spider-tronix/arboc/simulationExports/gazebo/stl/end.stl

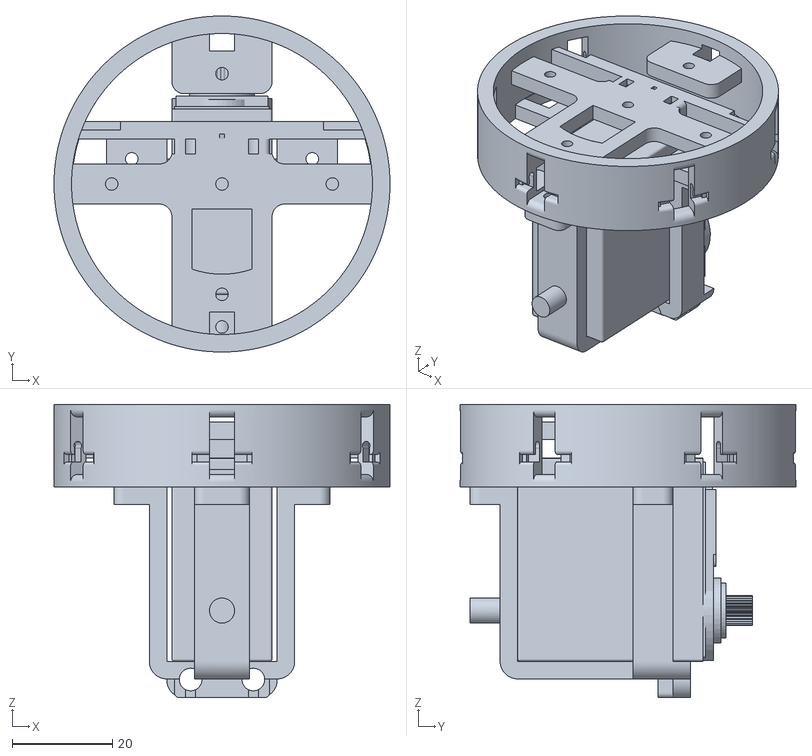
[picture p20: CAD file, 2019-06-01]
simulationExports/gazebo/stl/end.stl
67.0 x 67.0 x 58.5
