spider-tronix/arboc/mechanicalDesign/3DprintedParts/type4.step

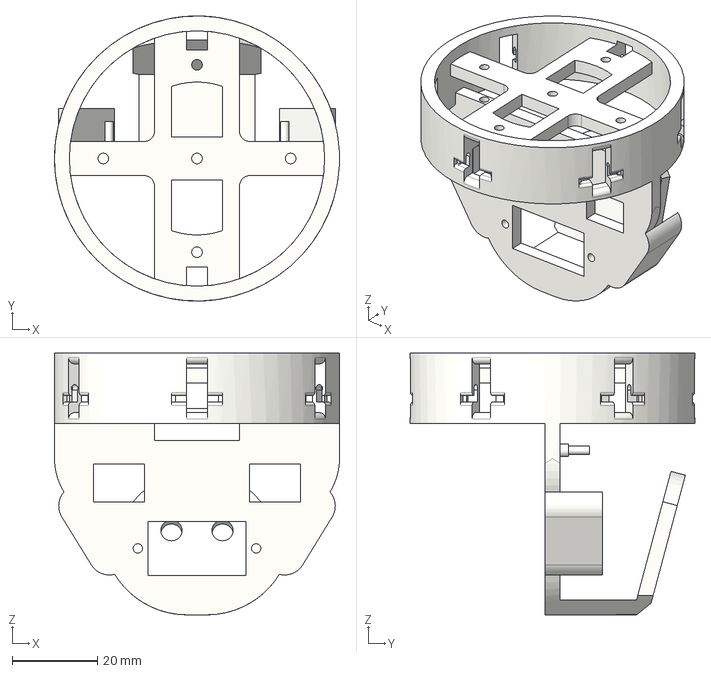
[picture p21: CAD file, 2019-06-01]
mechanicalDesign/3DprintedParts/type4.step
67.0 x 67.0 x 61.5 mm
