spider-tronix/arboc/mechanicalDesign/solidworks/iges/tailLink.SLDPRT

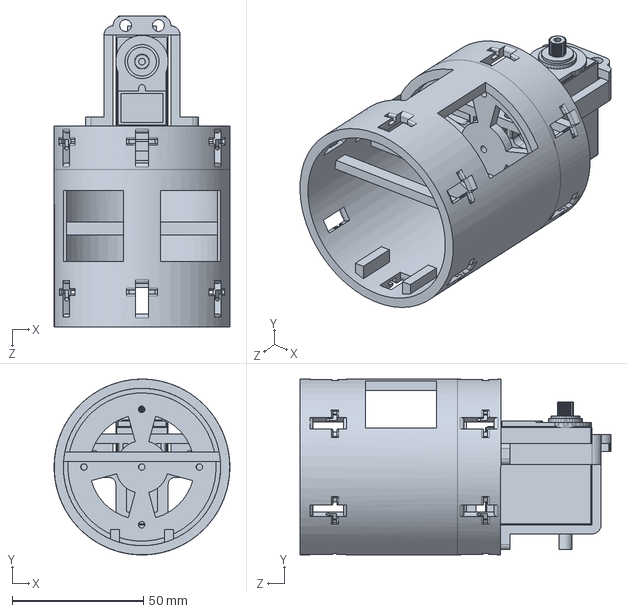
[picture p22: CAD file, 2019-06-01]
mechanicalDesign/solidworks/iges/tailLink.SLDPRT
67.0 x 67.0 x 118.5 mm
