spider-tronix/arboc/mechanicalDesign/solidworks/step/lowerBracket.step

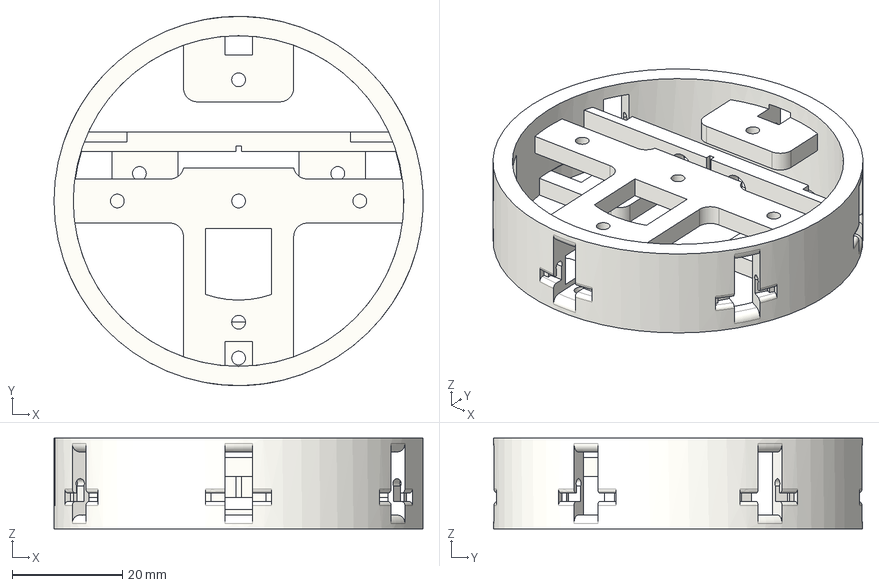
[picture p23: CAD file, 2019-06-01]
mechanicalDesign/solidworks/step/lowerBracket.step
67.0 x 67.0 x 16.5 mm
