spider-tronix/arboc/simulationExports/vrep/stl/moduleCollider.stl

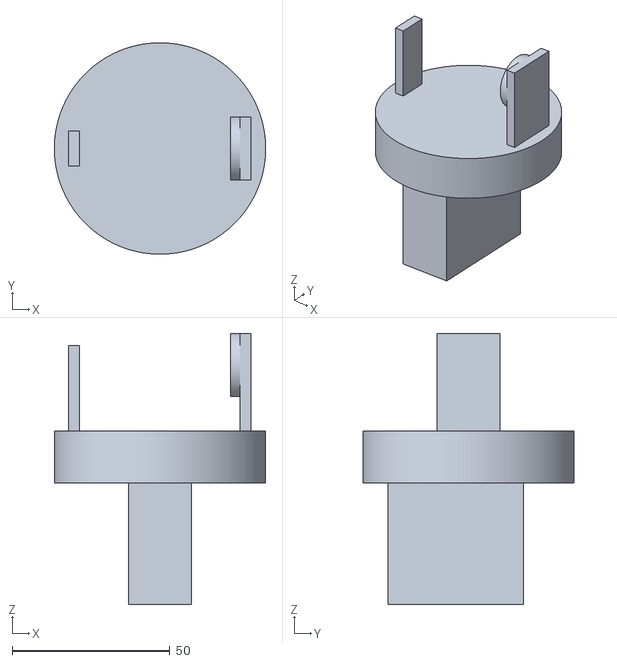
[picture p24: CAD file, 2019-06-01]
simulationExports/vrep/stl/moduleCollider.stl
67.0 x 67.0 x 85.9
