spider-tronix/arboc/mechanicalDesign/3DprintedParts/type2.step

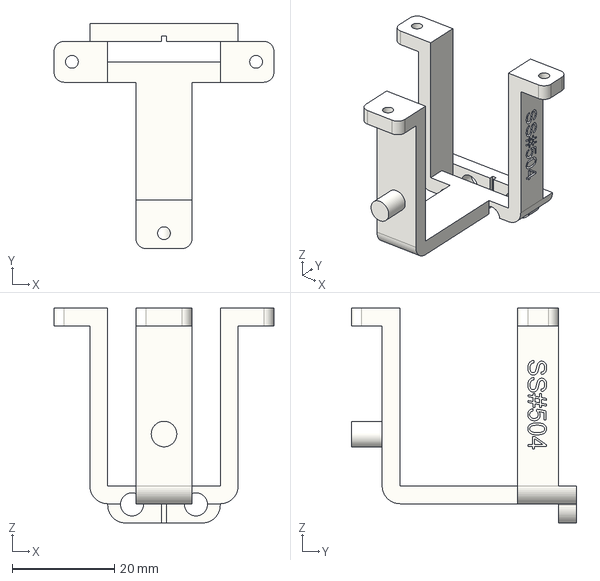
[picture p25: CAD file, 2019-06-01]
mechanicalDesign/3DprintedParts/type2.step
43.0 x 44.0 x 42.0 mm
