spider-tronix/arboc/mechanicalDesign/solidworks/sldprt/head.SLDPRT

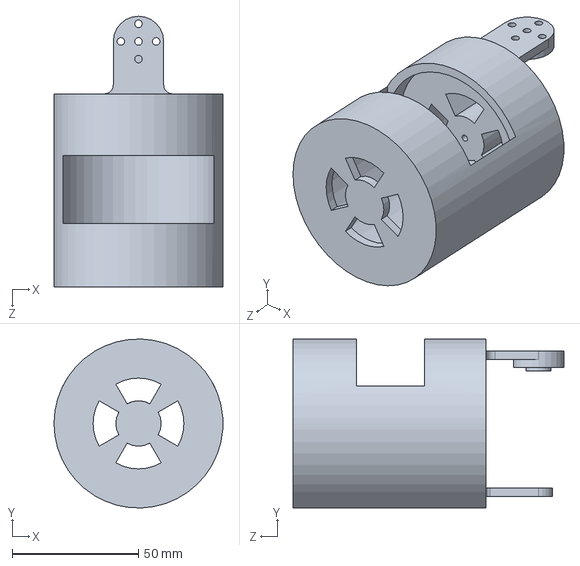
[picture p26: CAD file, 2019-06-01]
mechanicalDesign/solidworks/sldprt/head.SLDPRT
67.0 x 67.0 x 107.3 mm
