spider-tronix/arboc/mechanicalDesign/solidworks/step/middleBracket.step

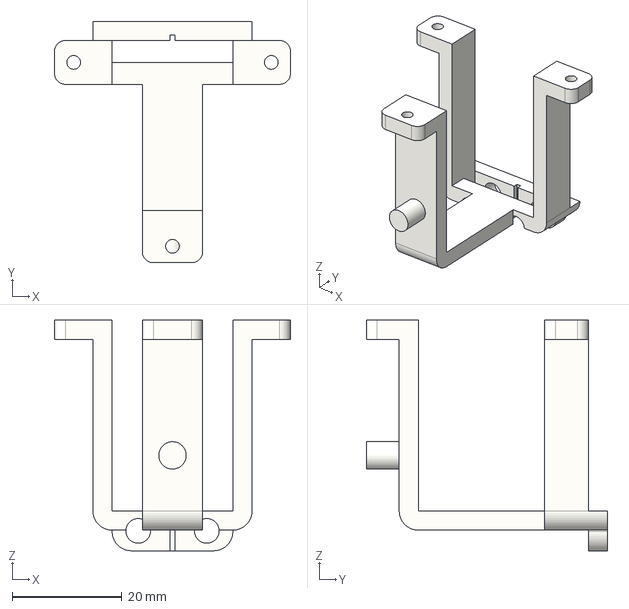
[picture p27: CAD file, 2019-06-01]
mechanicalDesign/solidworks/step/middleBracket.step
43.0 x 44.0 x 42.0 mm
