spider-tronix/arboc/simulationExports/gazebo/stl/topModule.stl

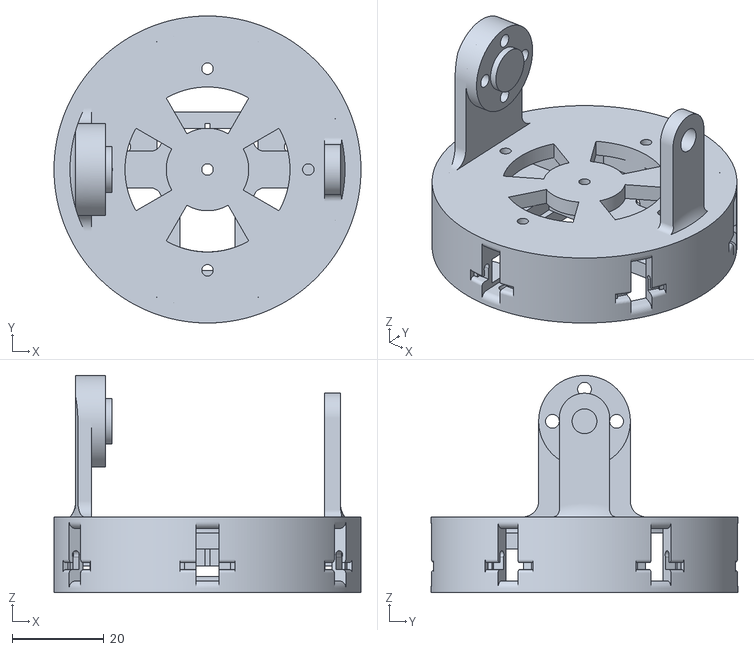
[picture p28: CAD file, 2019-06-01]
simulationExports/gazebo/stl/topModule.stl
67.0 x 67.0 x 47.4
