spider-tronix/arboc/mechanicalDesign/3DprintedParts/type6.step

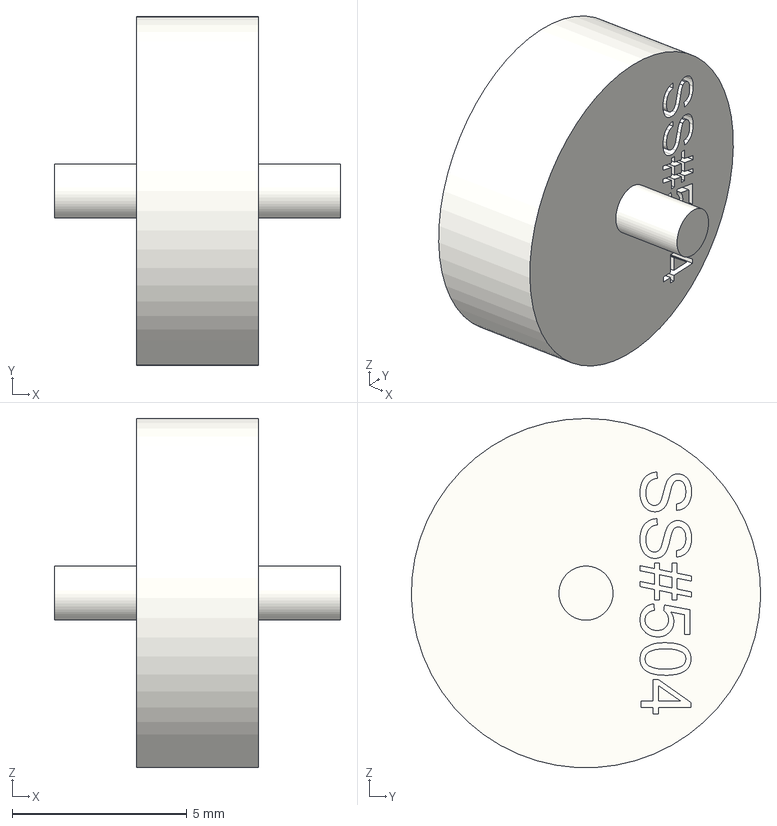
[picture p29: CAD file, 2019-06-01]
mechanicalDesign/3DprintedParts/type6.step
8.20 x 10.00 x 9.99 mm
