spider-tronix/arboc/mechanicalDesign/solidworks/sldprt/headMod.SLDPRT

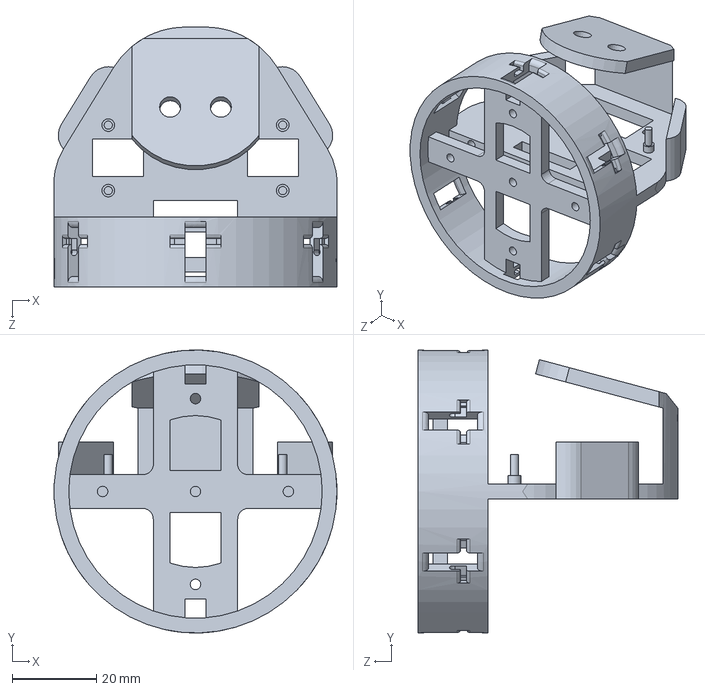
[picture p30: CAD file, 2019-06-01]
mechanicalDesign/solidworks/sldprt/headMod.SLDPRT
67.0 x 67.0 x 61.5 mm
