spider-tronix/arboc/simulationExports/vrep/stl/tailCollider.stl

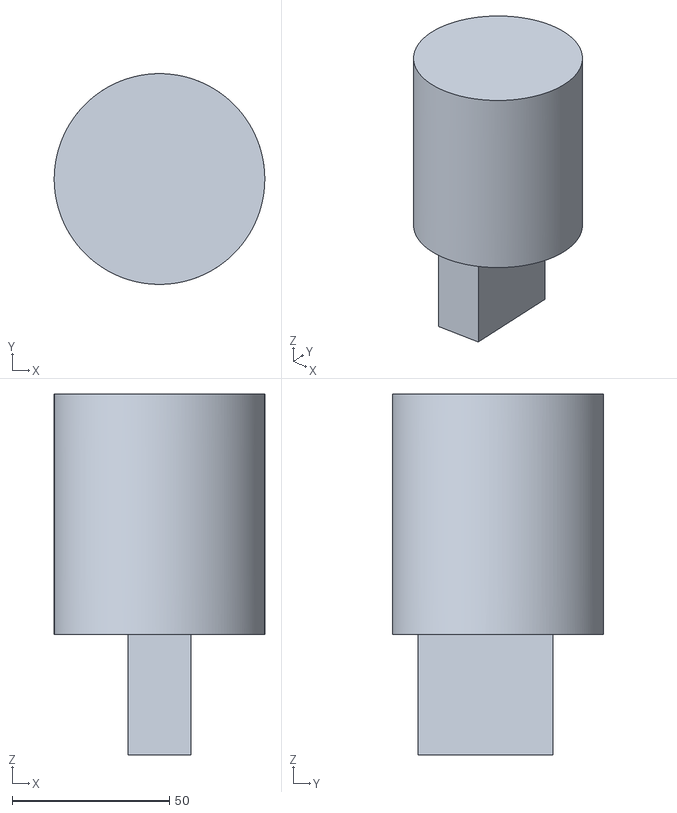
[picture p31: CAD file, 2019-06-01]
simulationExports/vrep/stl/tailCollider.stl
66.9 x 67.0 x 114.8
