spider-tronix/arboc/mechanicalDesign/solidworks/step/servo.step

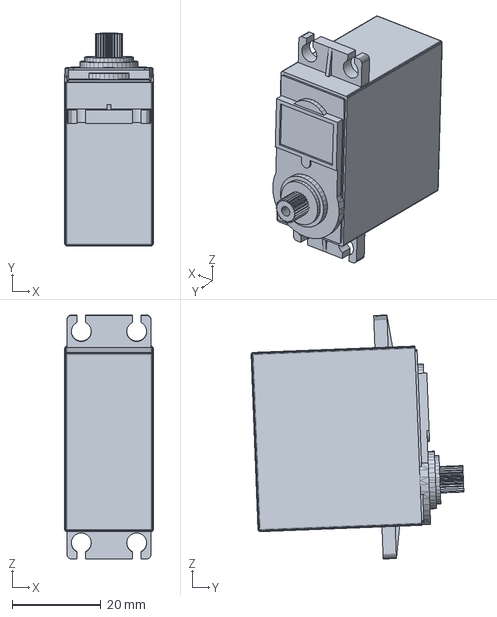
[picture p32: CAD file, 2019-06-01]
mechanicalDesign/solidworks/step/servo.step
20.0 x 48.1 x 55.1 mm
