spider-tronix/arboc/simulationExports/vrep/stl/headCollider.stl

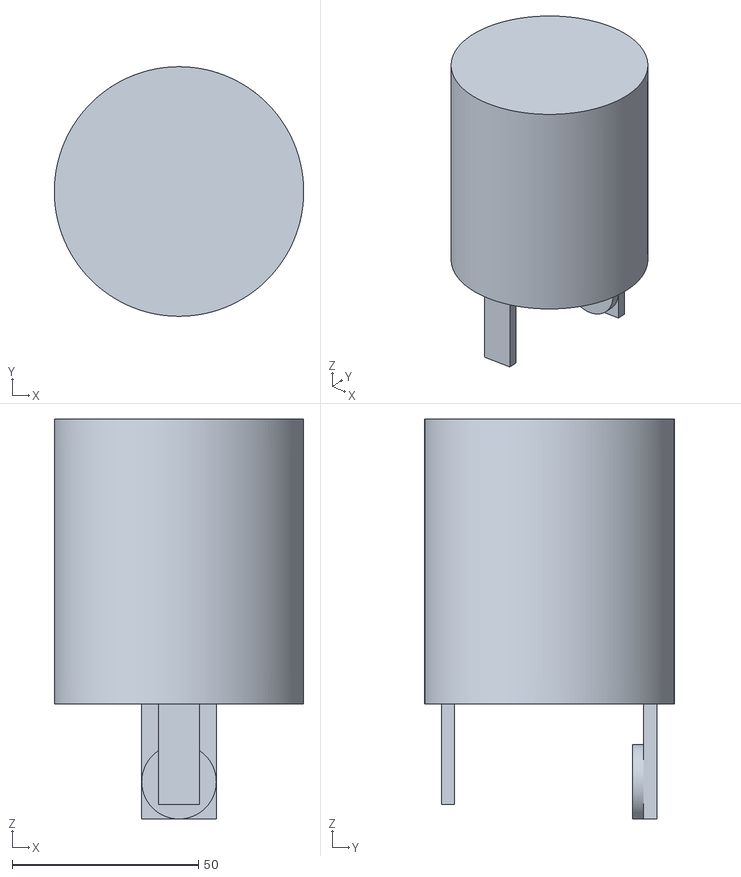
[picture p33: CAD file, 2019-06-01]
simulationExports/vrep/stl/headCollider.stl
66.9 x 67.0 x 107.4
