spider-tronix/arboc/mechanicalDesign/solidworks/step/upperBracket.step

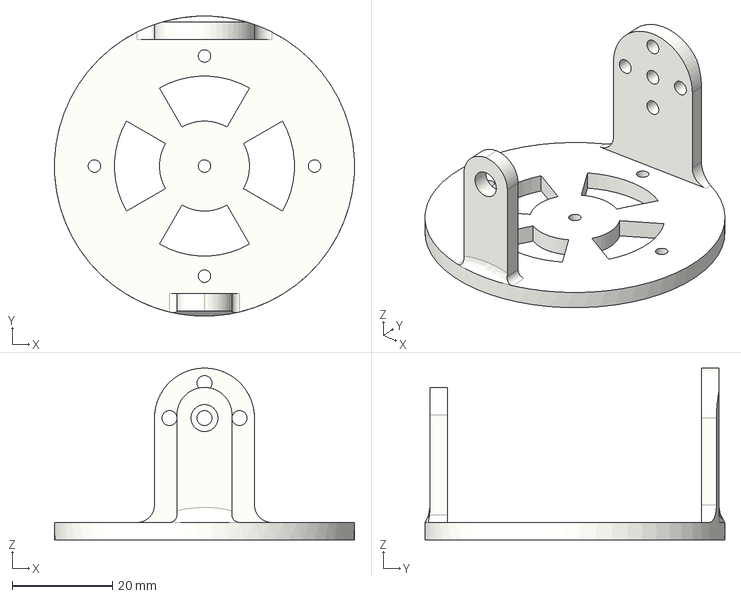
[picture p34: CAD file, 2019-06-01]
mechanicalDesign/solidworks/step/upperBracket.step
60.0 x 60.0 x 34.4 mm
